whileman133/uDummyLoad/4_Electrical/_python/spice/peak_detector.asc

C1: cap; 5.6n
C2: cap; 5.6n
C3: cap; 1µ
D1: schottky; BAT46WJ
I1: current; 2m
L1: ind; 5n
L2: ind; 5n
L3: ind; 1n
R1: res; 0.03
R2: res; 0.03
R3: res; 10
R4: res; 0.01
V1: voltage; SINE(0 45 {f})
Named nets: out, in, 0
.param f=30Meg
.tran 50m
;.step param f list 10Meg 30Meg 50Meg
