whileman133/uDummyLoad/4_Electrical/_python/spice/peak_detector_diode_comp.asc

C1: cap; 5.6n
C2: cap; 5.6n
C3: cap; 10p
D1: schottky; BAT46WJ
D2: schottky; BAT46WJ
R1: res; 100k
R3: res; 100k
R4: res; 10k
V1: voltage; SINE(0 45 {f})
Named nets: out, in, 0, D
.param f=10Meg
.tran 100u
.temp 40
