whileman133/uDummyLoad/4_Electrical/_python/spice/peak_detector_diode_comp_ver3.asc

C2: cap; 10n
C3: cap; 10p
D1: schottky; RB705D
R3: res; 100k
R4: res; 10k
V1: voltage; SINE(0 {Vpk} {f})
Named nets: out, in, 0
.param f=10Meg Vpk=10
.tran 100u
.ic V(out)={Vpk-0.3}
