whileman133/uDummyLoad/4_Electrical/_python/spice/peak_detector_double_diode.asc

C1: cap; 5.6n
C2: cap; 5.6n
D1: schottky; BAT46WJ
D2: schottky; BAT46WJ
L1: ind; 20n
L5: ind; 1n
V1: voltage; SINE(0 10 {f})
Named nets: out, in, 0
.param f=30Meg
.tran 500u
;.step param R list 100m 100Gig
