whileman133/uDummyLoad/4_Electrical/_python/spice/peak_detector_ideal.asc

C1: cap; 5.6n
C2: cap; 5.6n
C3: cap; 10p
D1: schottky; BAT46WJ
L1: ind; 20n
L2: ind; 5n
L5: ind; 5n
R1: res; 0.02
R2: res; 0.02
R3: res; 100k
R4: res; 10k
V1: voltage; SINE(0 10 {f})
Named nets: out, in, 0
.param f=2Meg
.tran 50u
