whileman133/uDummyLoad/4_Electrical/_python/spice/peak_detector_power_error_calc.asc

C1: cap; 5.6n
C2: cap; 5.6n
C3: cap; 10p
C4: cap; 11µ
D1: schottky; BAT46WJ
D2: schottky; BAT46WJ
D3: schottky; BAT46WJ
I1: current; 2m
L1: ind; 5n
L2: ind; 5n
L3: ind; 20n
R1: res; 100k
R2: res; 10
R3: res; 100k
R4: res; 10k
R5: res; 50
R6: res; 0.02
R7: res; 0.02
V1: voltage; SINE(0 45 {f})
Named nets: out, in, 0
.param f=7Meg
.tran 4m
