whileman133/uDummyLoad/4_Electrical/_python/spice/peak_detector_rev3.asc

C1: cap; 5.6n
C2: cap; 100p
C3: cap; 1µ
Csamp: cap; 10p
D1: schottky; BAT46WJ
I1: current; 2m
L1: ind; 5n
L2: ind; 5n
L3: ind; 1n
L4: ind; 20n
L5: ind; 10n
L6: ind; 10n
R1: res; 0.03
R2: res; 0.2
R3: res; 10
R4: res; 0.01
R5: res; 100k
R6: res; 10k
V1: voltage; SINE(0 45 {f})
Named nets: out, in, det, 0
.param f=30Meg
.tran 500u
;.step param f list 10Meg 30Meg 50Meg
