whileman133/uDummyLoad/4_Electrical/_python/spice/peak_detector_txline.asc

C1: cap; 10µ
D1: schottky; BAT46WJ
I1: current; 3m
R1: res; 50
T1: tline
V1: voltage; SINE(0 45 10Meg)
Named nets: 0, rftx, rfin, env
.tran 1m
