whileman133/uDummyLoad/4_Electrical/_python/spice/peak_detector_with_buffer.asc

C1: cap; 5.6n
C2: cap; 5.6n
C3: cap; 10p
D1: schottky; BAT46WJ
L1: ind; 20n
L2: ind; 5n
L3: ind; 5n
L5: ind; 5n
R1: res; 0.02
R2: res; 0.02
R3: res; {R}
R4: res; {R/10}
R5: res; 10
U1: UniversalOpamp2
V1: voltage; SINE(0 {Va} {f})
V2: voltage; 5
Named nets: out, in, 0, det
.param f=2Meg Va=30 R=30Meg
.tran 3m
.ic V(out)={Va}
